MrGeoTech/mefitis/pi/sensors/test_sensors.py

import pyaudio
import time
from math import log10
import audioop
import numpy as np

p = pyaudio.PyAudio()
WIDTH = 2
CHANNELS = 2
RATE = int(p.get_default_input_device_info()['defaultSampleRate'])
DEVICE = p.get_default_input_device_info()['index']

data_left = np.array([], dtype=np.int16)
data_right = np.array([], dtype=np.int16)
print(p.get_default_input_device_info())

def callback(in_data, frame_count, time_info, status):
    global data_left, data_right
    #print(in_data)
    #print("-" * 20)
    # Split stereo data into left and right mono streams
    audio_data = np.frombuffer(in_data, dtype=np.int16)
    print(audio_data)

    # Separate interleaved stereo channels
    left = audio_data[::2]
    right = audio_data[1::2]
    print(left)
    print(right)

    data_left = np.append(data_left, left)
    data_right = np.append(data_right, right)

    #print(left)
    #print(right)
    #print("-" * 30)
    
    # Calculate RMS for each channel
    #rms_left = audioop.rms(left, WIDTH) / 32767
    #rms_right = audioop.rms(right, WIDTH) / 32767
    #return in_data, pyaudio.paContinue


def calculate_rms(samples):
    return np.sqrt(np.mean(samples.astype(np.float32) ** 2))

stream = p.open(format=p.get_format_from_width(WIDTH),
                input_device_index=DEVICE,
                channels=CHANNELS,
                rate=RATE,
                input=True,
                output=False,
                stream_callback=callback)

stream.start_stream()

while stream.is_active():
    time.sleep(0.3)

    rms_left = calculate_rms(data_left)
    rms_right = calculate_rms(data_right)

    data_left = np.array([], dtype=np.int16)
    data_right = np.array([], dtype=np.int16)

    db_left = 20 * log10(rms_left) if rms_left > 0 else -float('inf')
    db_right = 20 * log10(rms_right) if rms_right > 0 else -float('inf')
    
    print(f"Left  - RMS: {rms_left:.4f}  DB: {db_left:.2f}")
    print(f"Right - RMS: {rms_right:.4f}  DB: {db_right:.2f}")
    print("-" * 40)

stream.stop_stream()
stream.close()
p.terminate()
